MelindaBirkenstock/TAS_kc/keycaps/sldprt/r0/r0_c0.SLDPRT

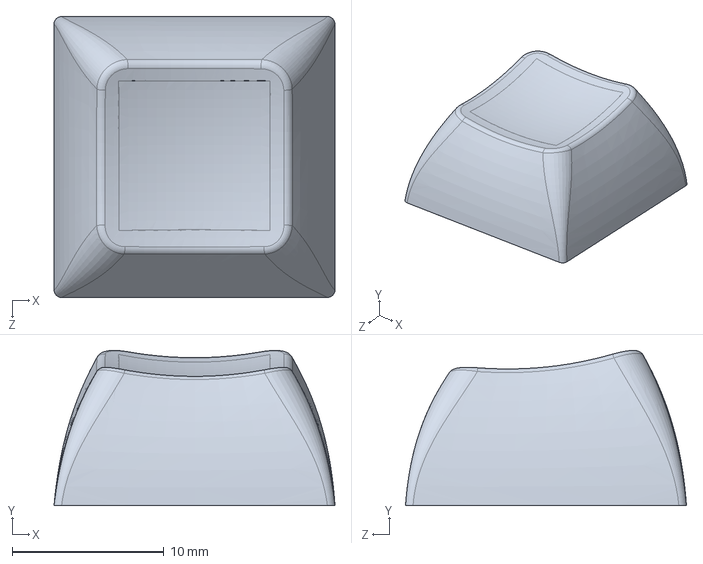
[picture p15: CAD file, 2020-01-01]
keycaps/sldprt/r0/r0_c0.SLDPRT
18.5 x 10.2 x 18.5 mm
