MelindaBirkenstock/TAS_kc/keycaps/sldprt/r1/r1_c3.SLDPRT

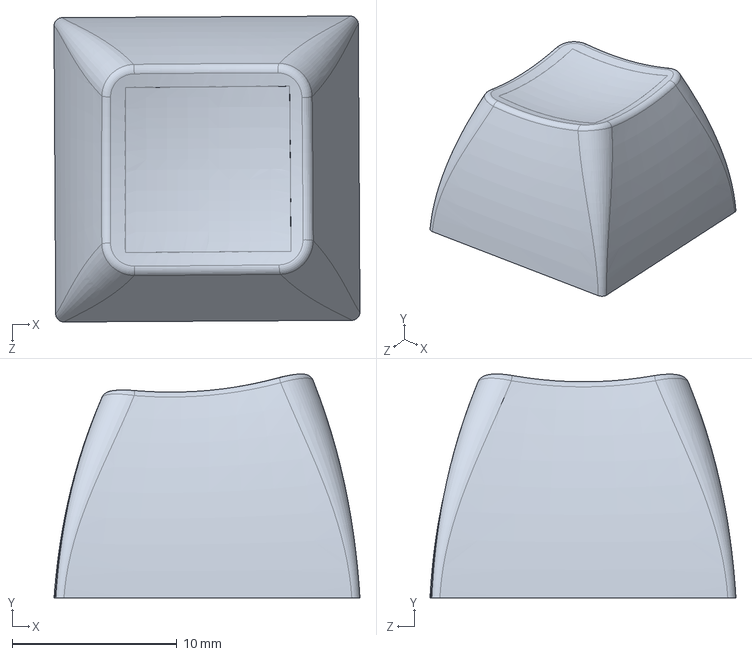
[picture p16: CAD file, 2020-01-01]
keycaps/sldprt/r1/r1_c3.SLDPRT
18.6 x 13.6 x 18.6 mm
