MelindaBirkenstock/TAS_kc/mx_stem_grid_4x6_b.SLDPRT

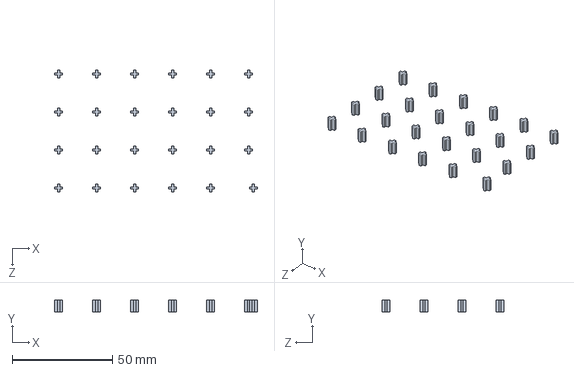
[picture p17: CAD file, 2020-01-01]
mx_stem_grid_4x6_b.SLDPRT
101.5 x 6.00 x 61.1 mm
