MelindaBirkenstock/TAS_kc/keycaps/sldprt/r1/r1_c4.SLDPRT

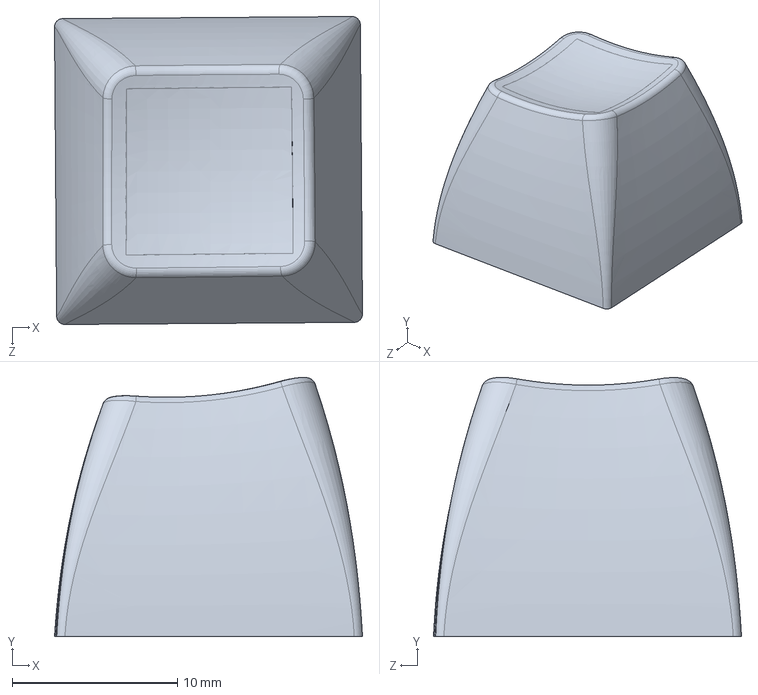
[picture p18: CAD file, 2020-01-01]
keycaps/sldprt/r1/r1_c4.SLDPRT
18.6 x 15.7 x 18.6 mm
