MelindaBirkenstock/TAS_kc/mx_stem_grid_6x6.SLDPRT

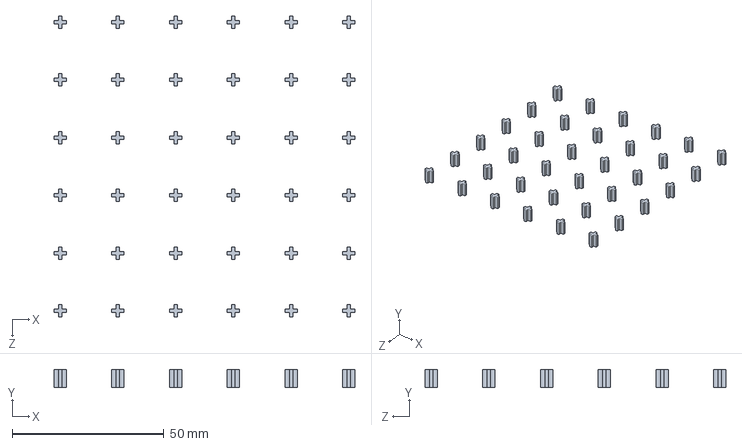
[picture p19: CAD file, 2020-01-01]
mx_stem_grid_6x6.SLDPRT
99.1 x 6.00 x 99.1 mm
